jes/scamp-cpu/pdf/8250.jpeg

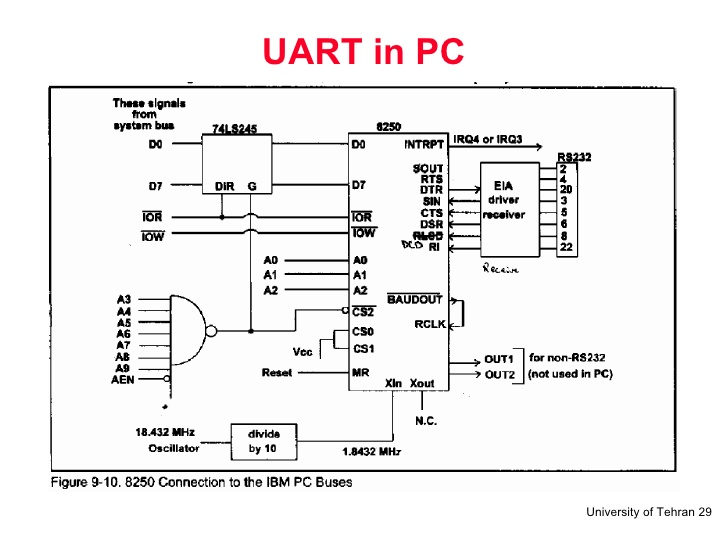
pdf/8250.jpeg
