jes/scamp-cpu/verilog/cpu_tb.v

/* CPU testbench */
`include "cpu.v"

module test;
    reg clk;
    reg reset_bar = 1;
    wire [15:0] addr;
    wire [15:0] bus;

    CPU cpu (clk, reset_bar, addr, bus, DI, DO);

    reg [15:0] cycle = 0;

    parameter EXPECT_OUTPUTS = 25;
    reg [15:0] outputs = 0;

    initial begin
        reset_bar = 0; clk = 0;
        #1 clk = 1;
        #1 clk = 0; reset_bar = 1;

        #100

        /* run the CPU for 3000 cycles */
        while (cycle < 3000) begin
            cycle = cycle + 1;

            #1 clk = 1;

            #1 if (addr == 0 && DI) begin
                if (bus !== outputs) $display("Bad: output ",outputs, " != ", outputs, ": ", bus);
                outputs = outputs + 1;
            end

            clk = 0;
        end

        if (outputs !== EXPECT_OUTPUTS) $display("Bad: got ", outputs, " outputs, expected ", EXPECT_OUTPUTS);
    end
endmodule
