jes/scamp-cpu/verilog/ttl-memory.v

/* Memory

   When "en" is 1, gives current value to the bus
   When "load" is 1 and clock edge rises, RAM takes in new value from the bus
*/

`include "ttl/7400.v"
`include "ttl/7432.v"
`include "ttl/at28c16.v"
`include "ttl/w24512a.v"

module Memory(clk, bus, load, en, address);
    input clk;
    inout [15:0] bus;
    input load;
    input en;
    input [15:0] address;

    at28c16 #(.ROM_FILE("testrom-low.hex"), .ROM_BYTES(256)) rom1 ({3'b0, address[7:0]}, bus[7:0], romen_bar, 1'b0);
    at28c16 #(.ROM_FILE("testrom-high.hex"), .ROM_BYTES(256)) rom2 ({3'b0, address[7:0]}, bus[15:8], romen_bar, 1'b0);

    w24512a ram1 (address, bus[7:0], 1'b0, 1'b1, load_clk_bar, ramen_bar);
    w24512a ram2 (address, bus[15:8], 1'b0, 1'b1, load_clk_bar, ramen_bar);

    // we want the RAM chip if any of the first 8 bits are 1, and the ROM
    // chip otherwise (i.e. ROM if address < 256, else RAM)
    ttl_7432 orer1 ({address[15], address[14], address[13], address[12]}, {address[11], address[10], address[9], address[8]}, {or1, or2, or3, or4});
    ttl_7432 orer2 ({1'bZ, or5, or1, or2}, {1'bZ, or6, or3, or4}, {nc, want_ram, or5, or6});

    // ramen_bar = want_ram NAND en
    // want_rom = want_ram NAND want_ram = !want_ram
    // romen_bar = want_rom NAND en
    ttl_7400 nander ({load, en, en, want_ram}, {clk, want_ram, want_rom, want_ram}, {load_clk_bar, ramen_bar, romen_bar, want_rom});
endmodule
