jes/scamp-cpu/verilog/fpga-cpu.v

/* CPU */

`include "fpga-alu.v"
`include "control.v"
`include "fpga-ucode.v"
`include "fr.v"
`include "fpga-ir.v"
`include "fpga-memory.v"
`include "fpga-pc.v"
`include "fpga-tstate.v"
`include "register.v"

`include "fpga-cpuimpl.v"
