jes/scamp-cpu/verilog/fpga-ir.v

/* Instruction register

   When "enl" is 1, gives val&0xff on to bus
   When "enh" is 1, gives 0xff00 + (val&0xff) on to bus
   When "load" is 1 and clock edge rises, takes in new value from the bus
   Always gives current value to 'value'
*/
module IR(clk, bus, load_bar, enl_bar, enh_bar, value);
    input clk;
    inout [15:0] bus;
    input load_bar;
    input enl_bar;
    input enh_bar;
    output [15:0] value;

    reg [15:0] val = 0;

    assign load = !load_bar;
    assign enl = !enl_bar;
    assign enh = !enh_bar;

    assign value = val;

    always @ (posedge clk) begin
        if (load) val <= bus;
    end
endmodule
