jes/scamp-cpu/verilog/ttl-cpu.v

/* CPU */

`include "ttl-alu.v"
`include "ttl-control.v"
`include "ttl-ucode.v"
`include "ttl-fr.v"
`include "ttl-ir.v"
`include "ttl-memory.v"
`include "ttl-pc.v"
`include "ttl-tstate.v"
`include "ttl-register.v"

`include "cpuimpl.v"
