jes/scamp-cpu/verilog/ttl/7404.v

// Hex inverter

`ifndef TTL_7404
`define TTL_7404

module ttl_7404 #(parameter BLOCKS = 6, DELAY_RISE = 0, DELAY_FALL = 0)
(
  input [BLOCKS-1:0] A,
  output [BLOCKS-1:0] Y
);

//------------------------------------------------//
reg [BLOCKS-1:0] computed;

always @(*)
begin
  computed = ~A;
end
//------------------------------------------------//

assign #(DELAY_RISE, DELAY_FALL) Y = computed;

endmodule

`endif
